alexdrymonitis/3dPd/circuits/module_generic_bottom_board/PDF/module_generic_bottom_board-top_side.pdf

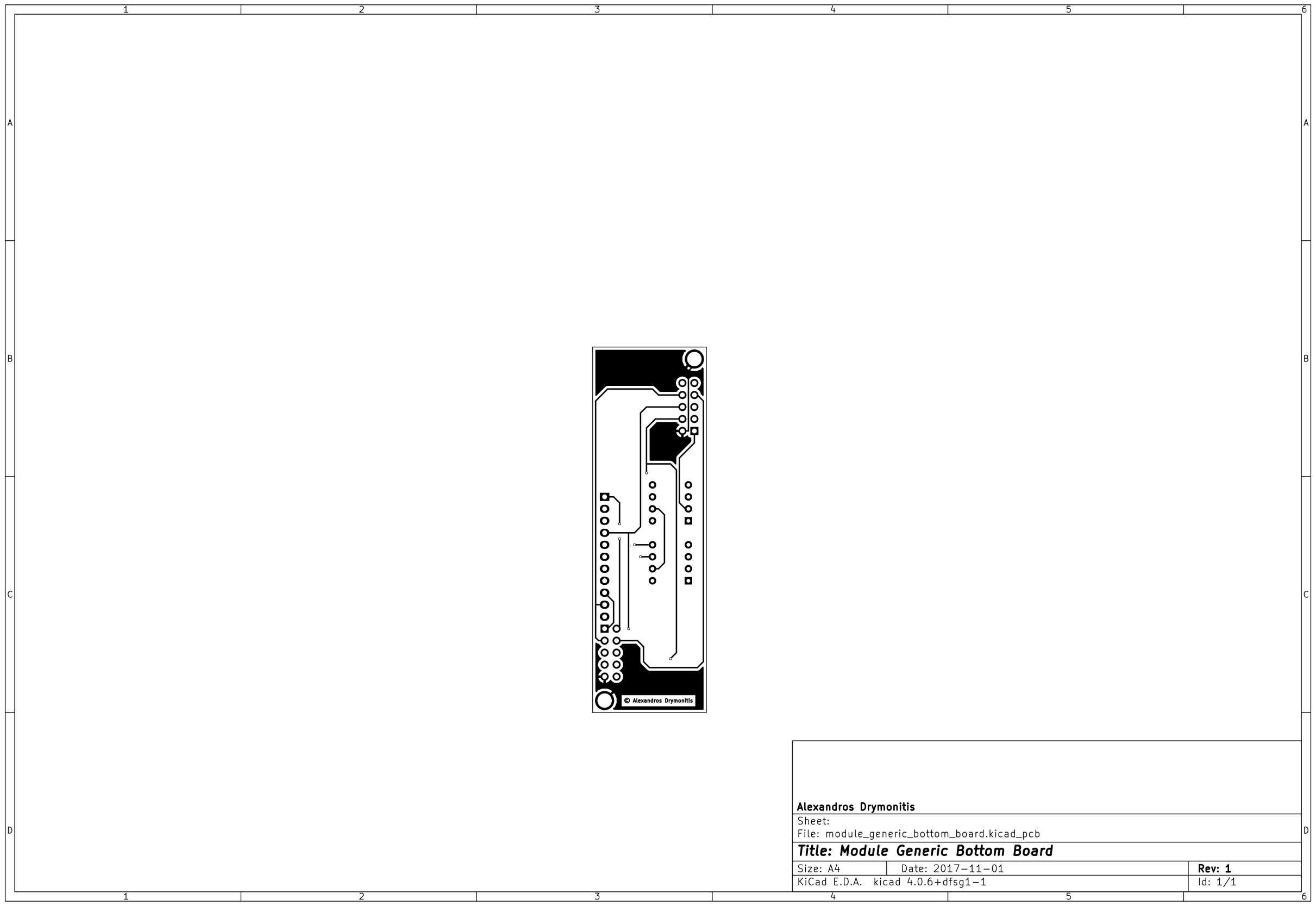
[picture p6: page 1]
