alexdrymonitis/3dPd/circuits/module_generic_top_board/PDF/module_generic_top_board-bottom_side.pdf

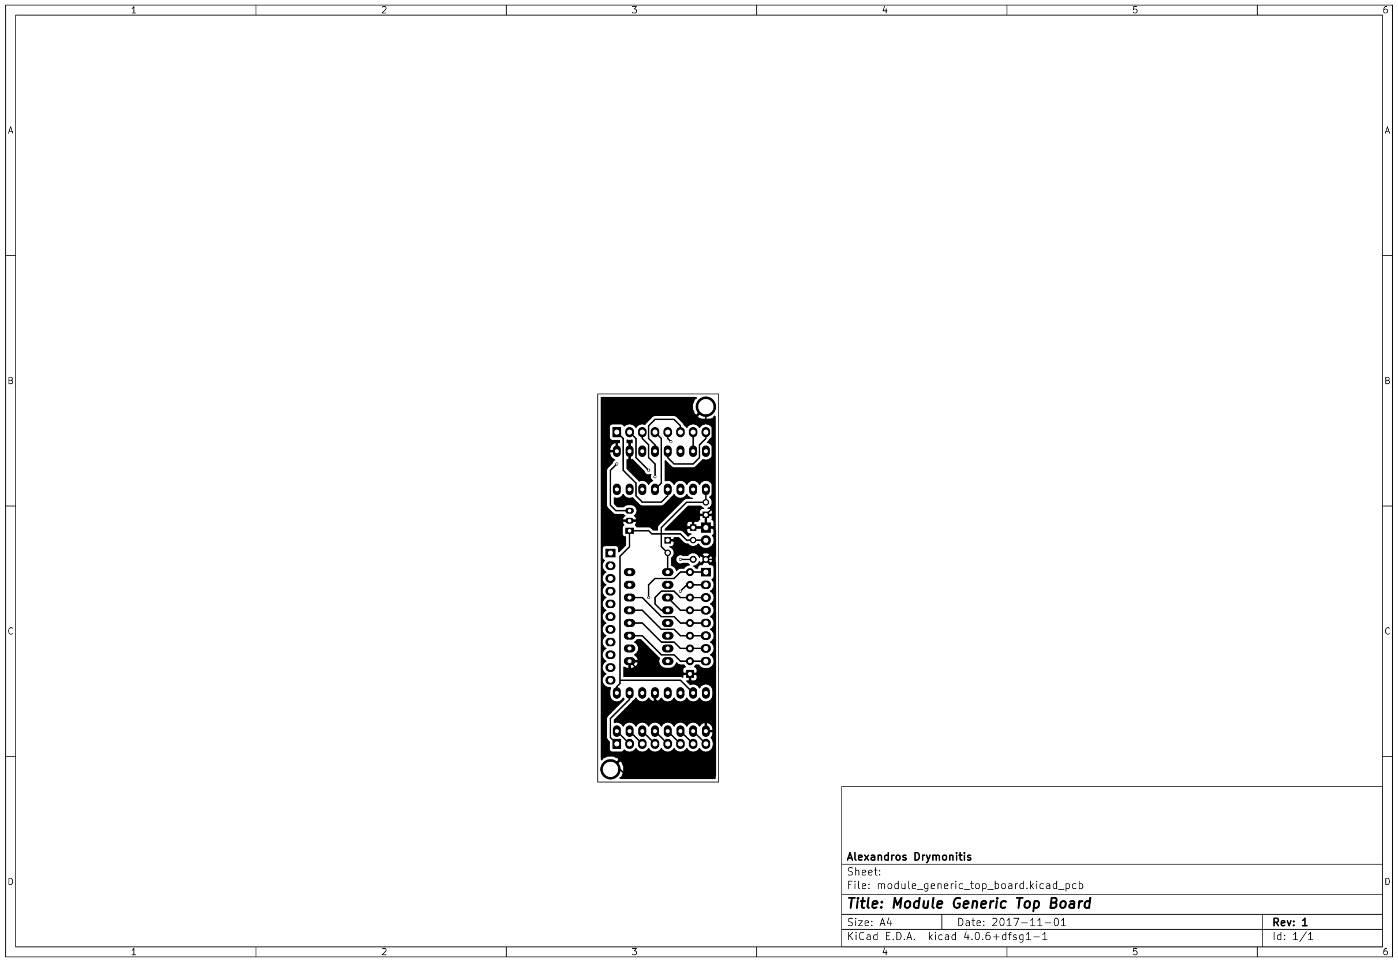
[picture p7: page 1]
