alexdrymonitis/3dPd/circuits/module_generic_top_board/PDF/module_generic_top_board-top_side.pdf

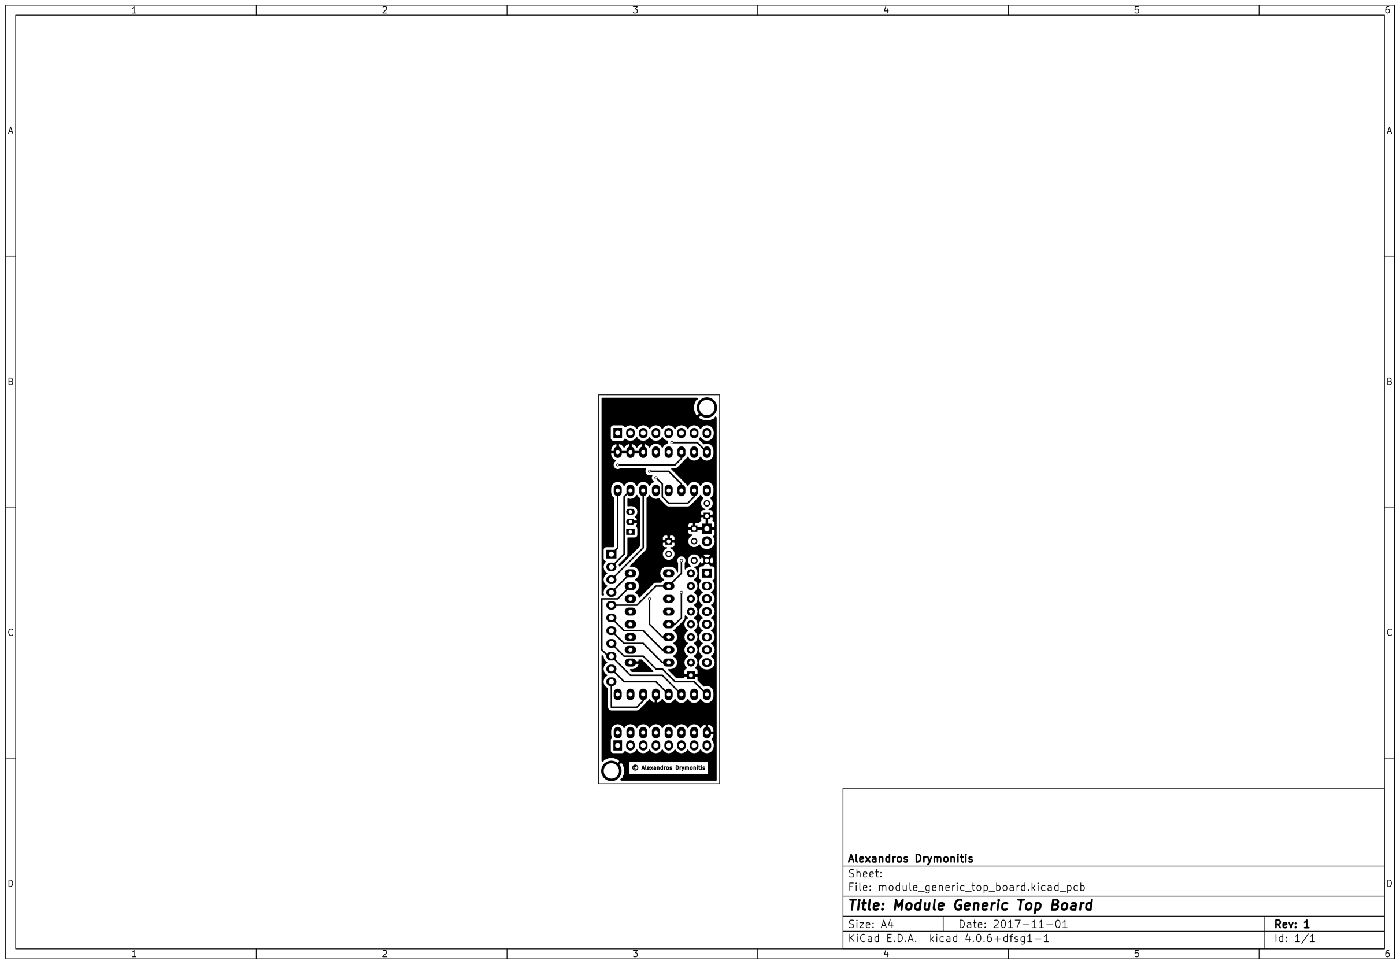
[picture p8: page 1]
