alexdrymonitis/3dPd/circuits/power_bus/PDF/power_bus.pdf

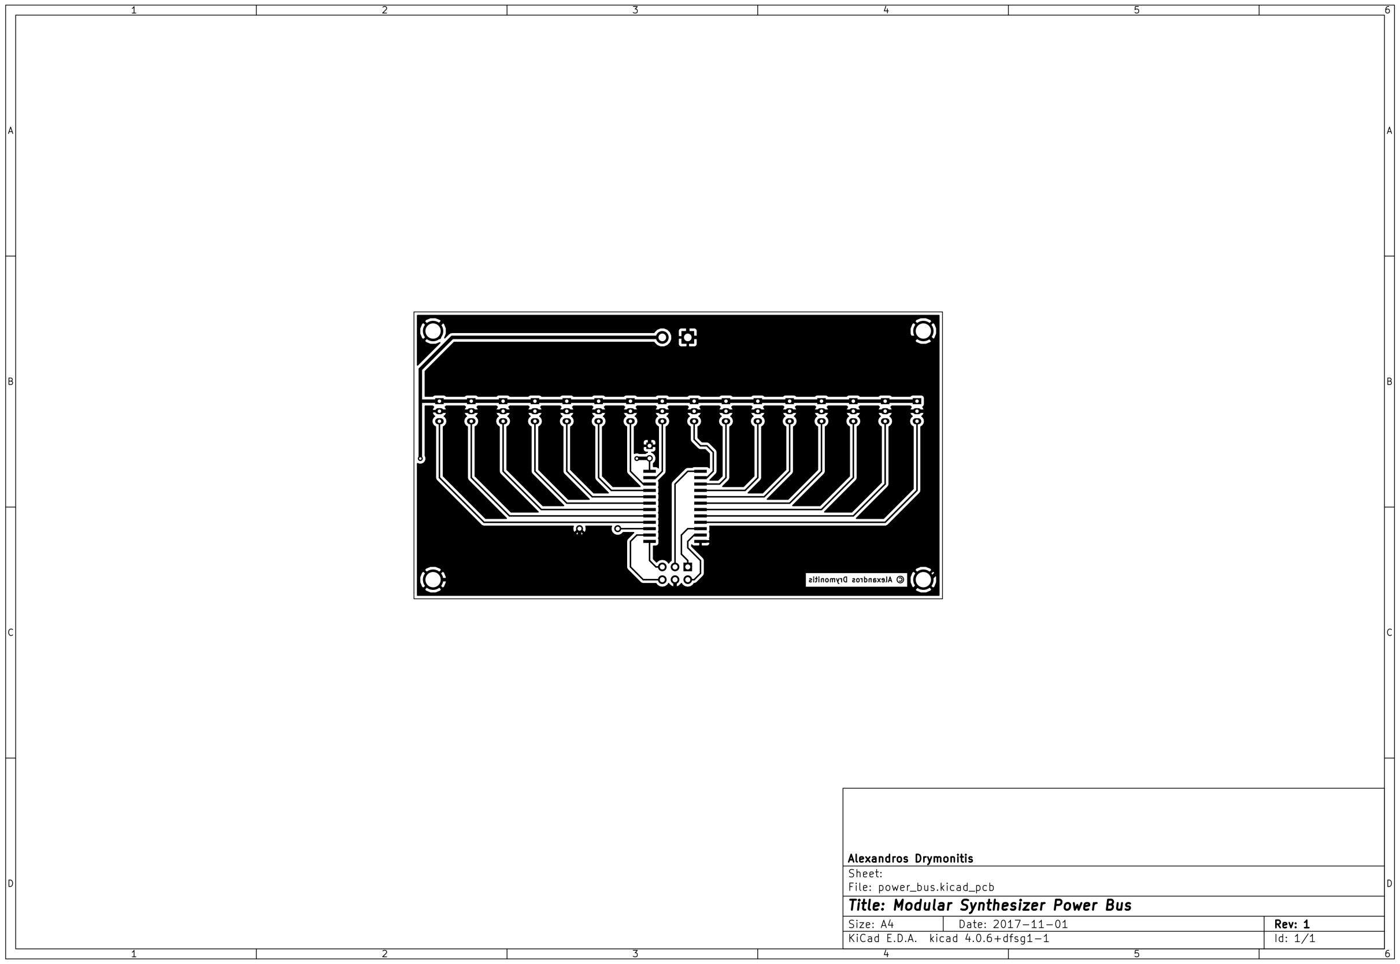
[picture p9: page 1]
