alexdrymonitis/3dPd/circuits/power_distributor/PDF/power_distributor.pdf

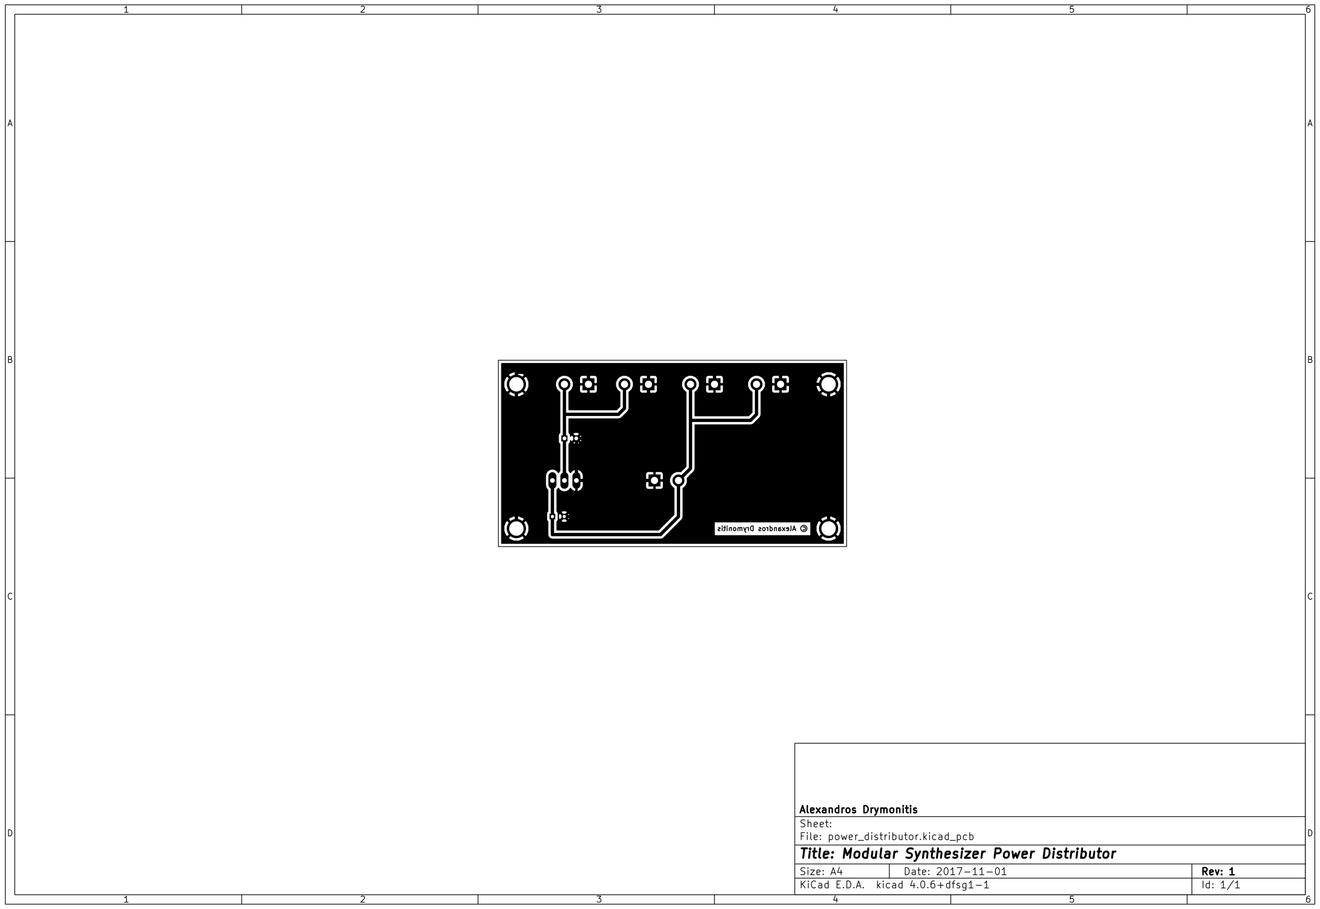
[picture p10: page 1]
