alexdrymonitis/3dPd/circuits/teensy_mother_board/PDF/teensy_mother_board.pdf

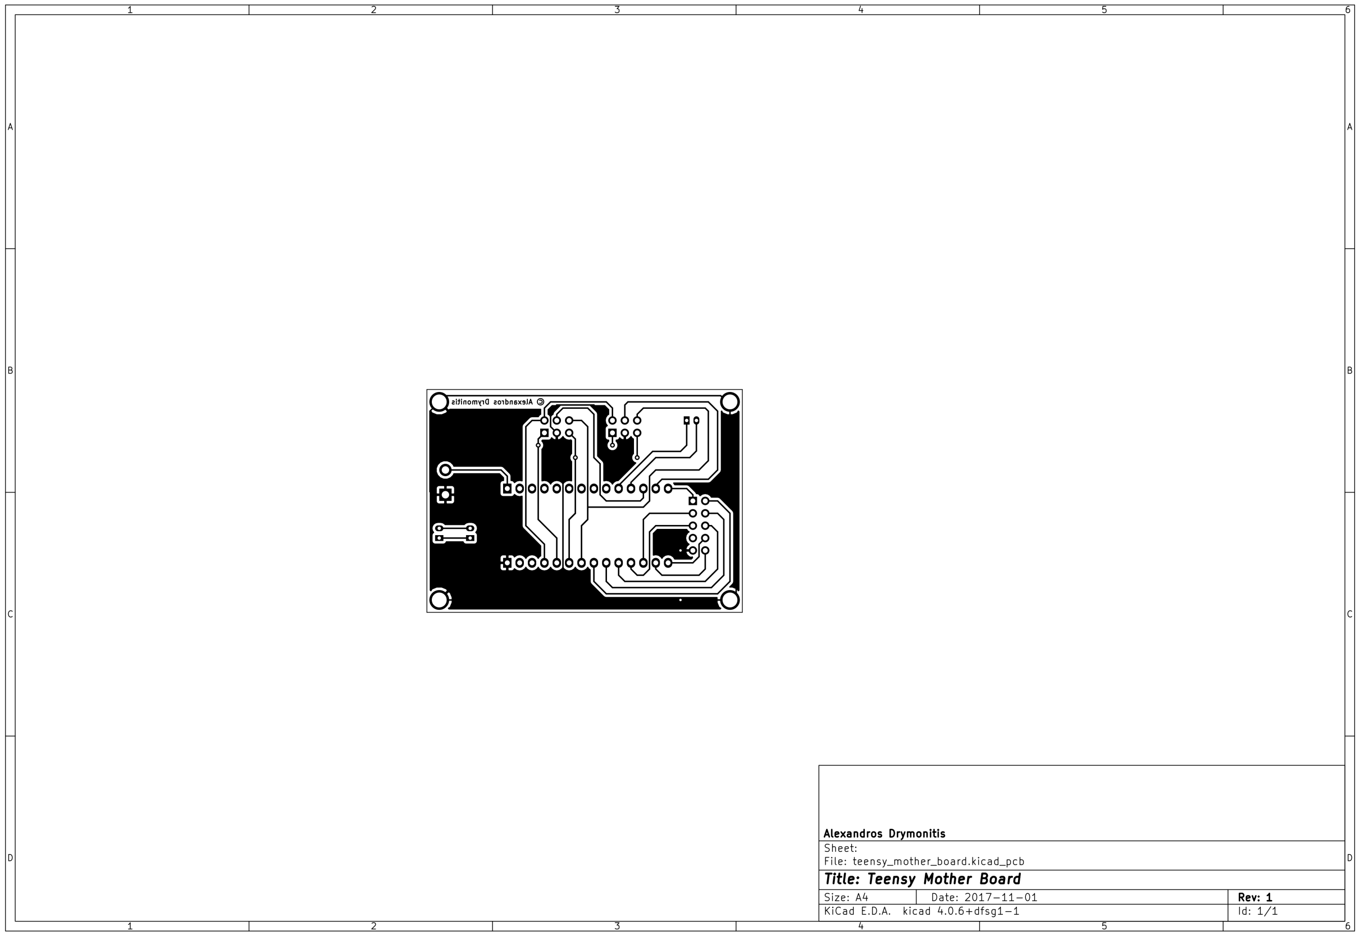
[picture p11: page 1]
